gravitymir/auto_probe/boards/STM32H723ZG-CoreBoard/sch.pdf

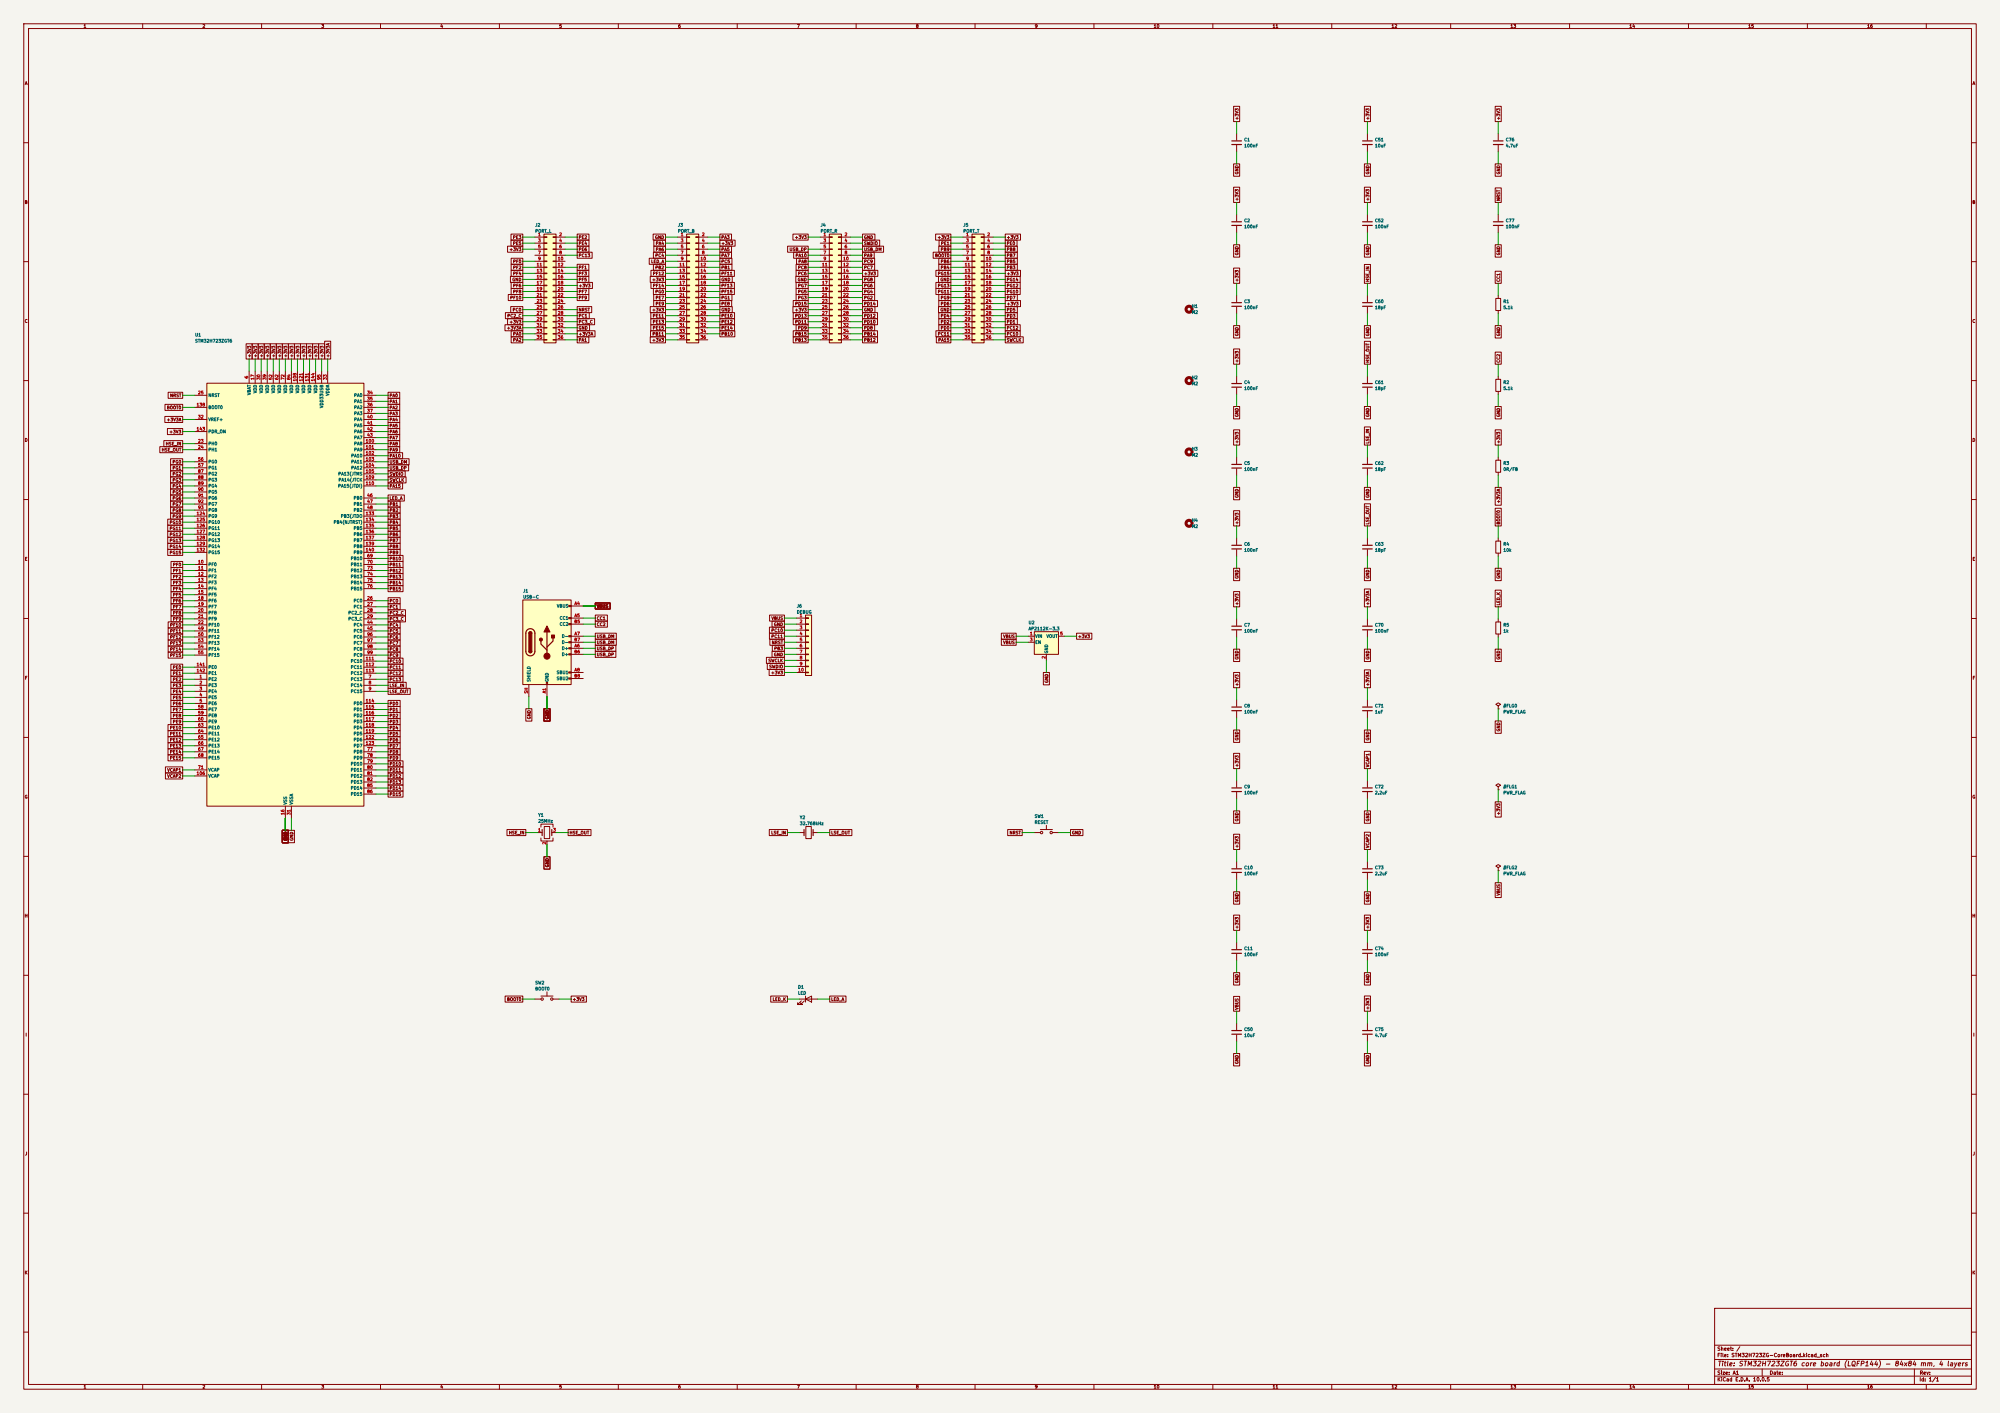
[picture p8: page 1]

Sheet: /
File: STM32H723ZG-CoreBoard.kicad_sch
Title: STM32H723ZGT6 core board (LQFP144) - 84x84 mm, 4 layers

Size: A1 | Rev:
KiCad E.D.A. 10.0.5 | Id: 1/1
