gravitymir/auto_probe/boards/STM32H723ZG-CoreBoard/bot.pdf

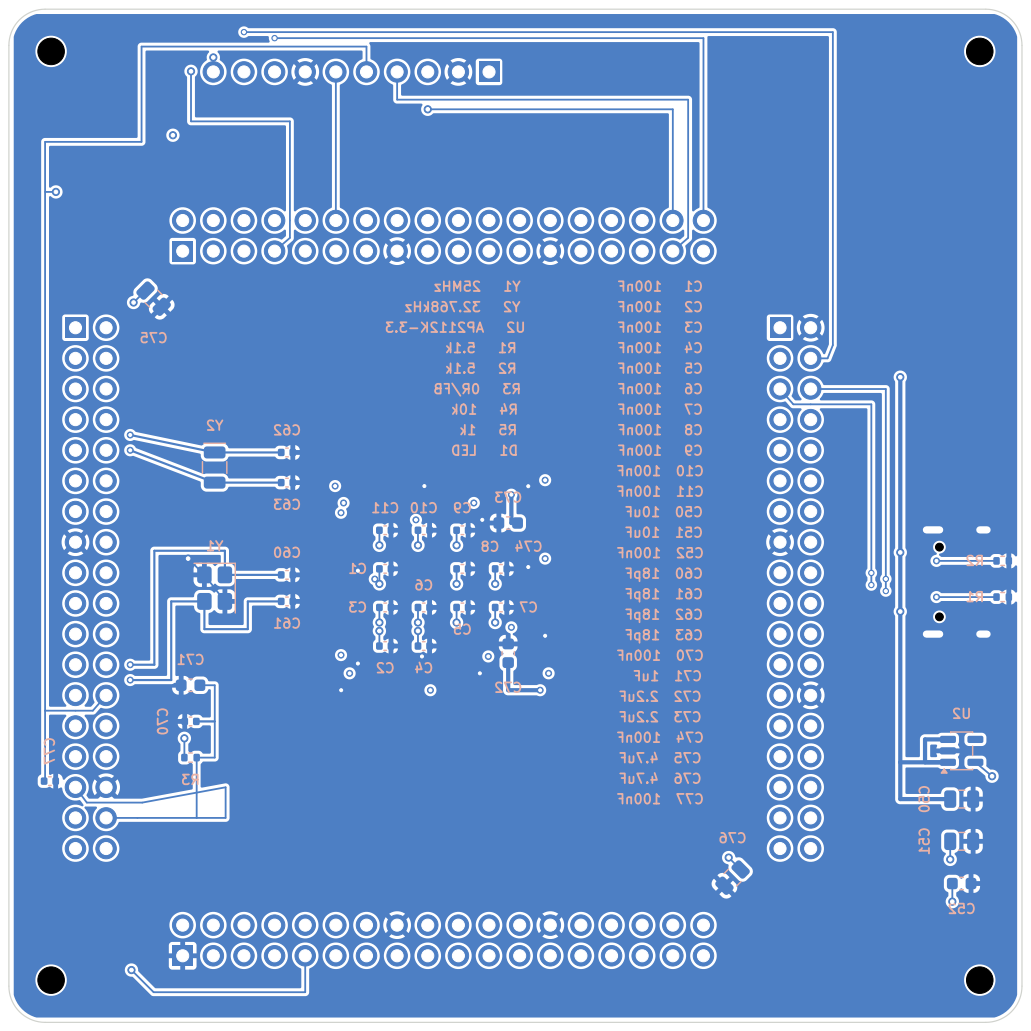
[picture p15: page 1]
