gravitymir/auto_probe/boards/STM32H723ZG-CoreBoard/top.pdf

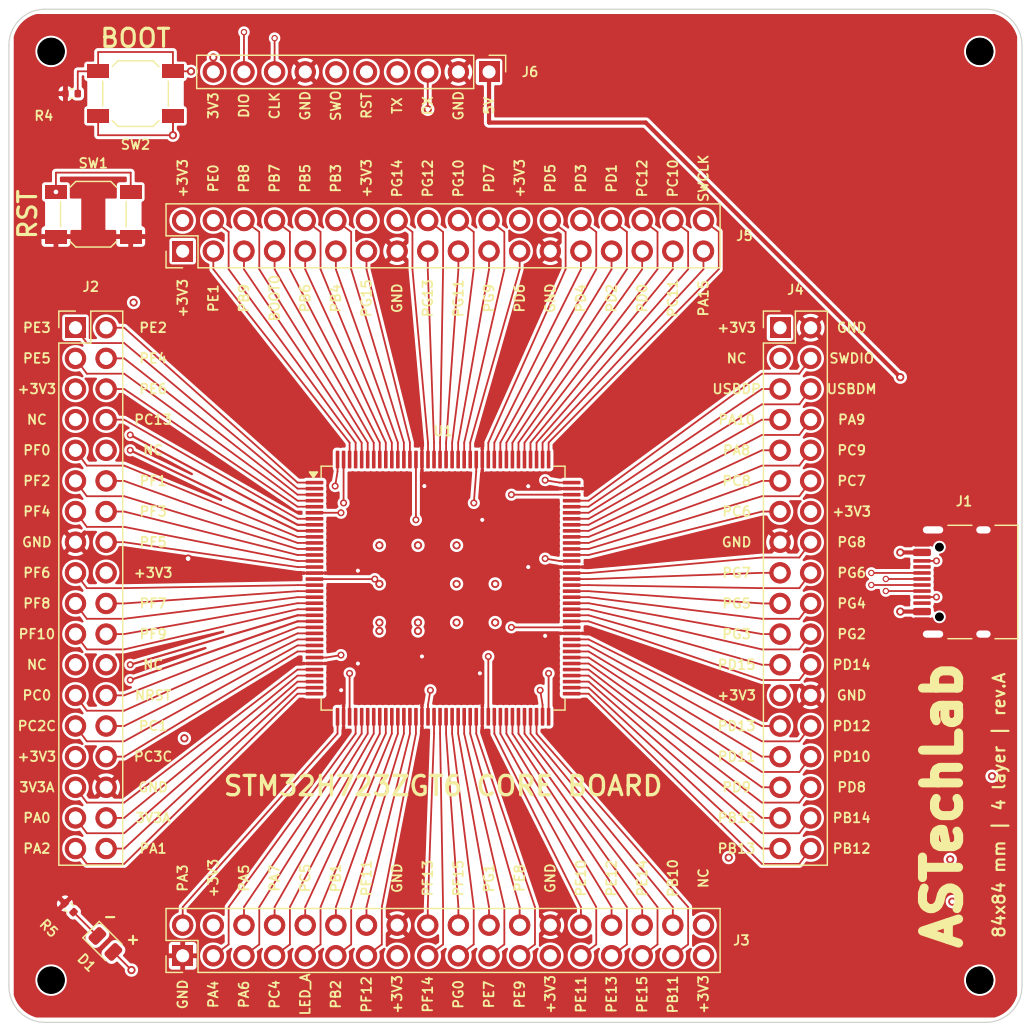
[picture p16: page 1]
